PiumiOshani/analog-volume-expander/images/screenshots/control voltage circuit.png

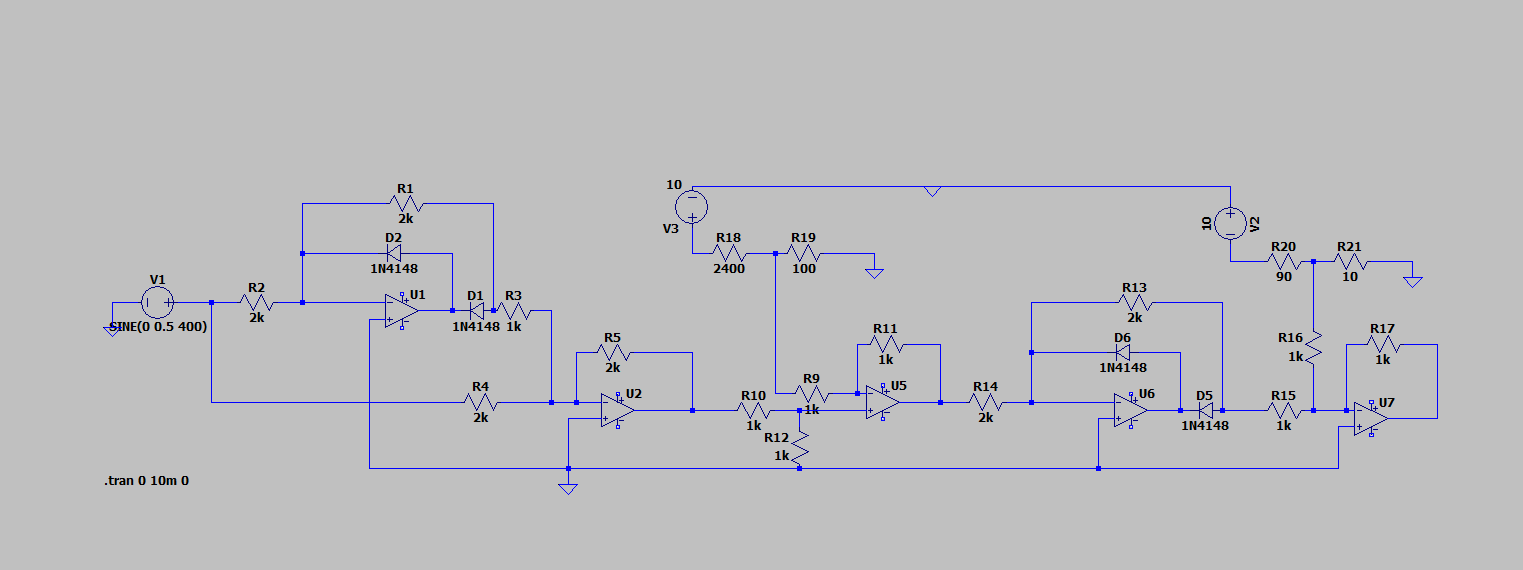
images/screenshots/control voltage circuit.png
