PiumiOshani/analog-volume-expander/images/screenshots/functional_block_diagram.png

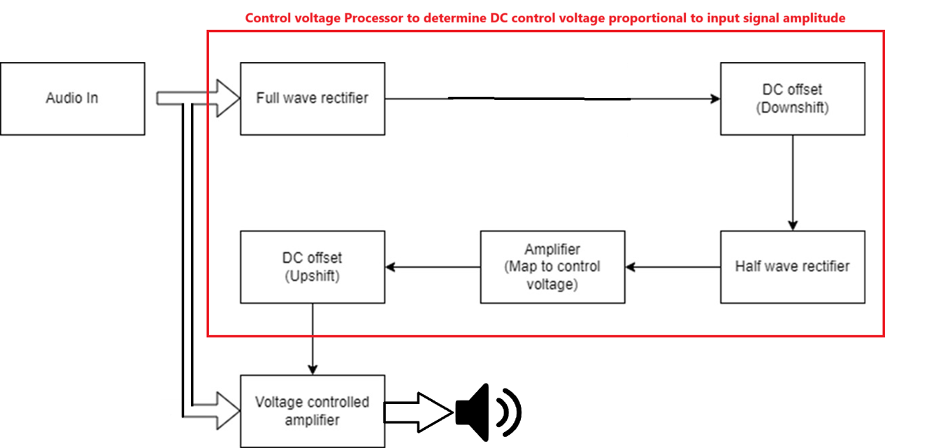
images/screenshots/functional_block_diagram.png
