PiumiOshani/analog-volume-expander/images/screenshots/notch filter.jpg

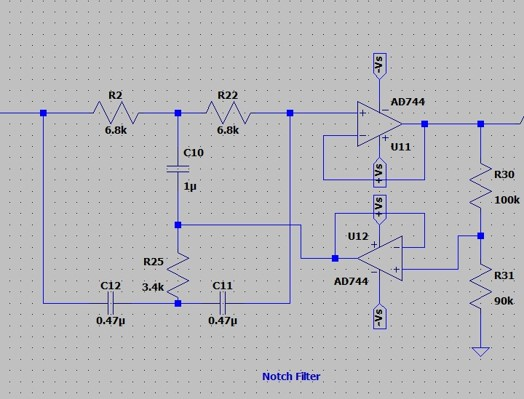
images/screenshots/notch filter.jpg
