PiumiOshani/analog-volume-expander/images/screenshots/VCA.png

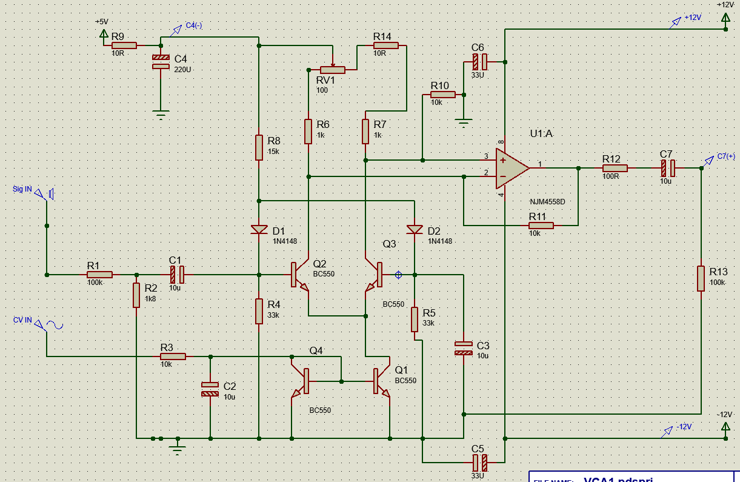
images/screenshots/VCA.png
