PiumiOshani/analog-volume-expander/images/hardware/PCB testing.png

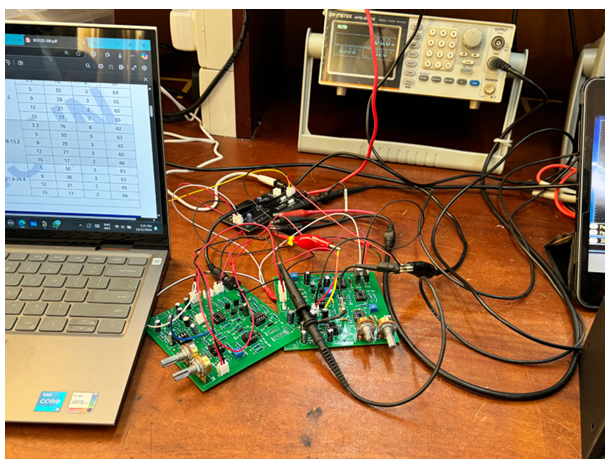
images/hardware/PCB testing.png
