PiumiOshani/analog-volume-expander/src/LTspice Simulations/Draft5.asc

C1: cap; 10µ
C2: cap; 10µ
C3: cap; 220µ
C4: cap; 10µ
C5: cap; 10µ
C6: cap; 1µ
C7: cap; 0.47µ
C8: cap; 0.47µ
D1: diode; 1N4148
D2: diode; 1N4148
D5: diode; 1N4148
D6: diode; 1N4148
M1: nmos
M2: nmos
Q1: npn
Q2: npn
R1: res; 2k
R2: res; 2k
R3: res; 1k
R4: res; 2k
R5: res; 2k
R6: res; 100
R7: res; 100k
R8: res; 100k
R9: res; 1k
R10: res; 1k
R11: res; 1k
R12: res; 1k
R13: res; 2k
R14: res; 2k
R15: res; 1k
R16: res; 1k
R17: res; 1k
R18: res; 2400
R19: res; 100
R20: res; 90
R21: res; 10
R22: res; 1k
R23: res; 20k
R24: res; 100k
R25: res; 100k
R26: res; 1k
R27: res; 1k
R28: res; 100k
R29: res; 1k
R30: res; 10
R31: res; 10k
R32: res; 10k
R33: res; 100
R34: res; 100k
R35: res; 6.8k
R36: res; 6.8k
R37: res; 3.3k
R38: res; 510
R39: res; 10k
U1: UniversalOpAmp
U2: UniversalOpAmp
U3: UniversalOpAmp
U4: UniversalOpAmp
U5: UniversalOpAmp
U6: UniversalOpAmp
U7: UniversalOpAmp
U8: UniversalOpAmp
U9: UniversalOpAmp
V1: voltage; SINE(0 0.5 400)
V2: voltage; 10
V3: voltage; 10
V4: voltage; 5
Named nets: 0
.tran 0 20m 10m
